juchong/ADXRS450-FRC-Gyro-Board/Documentation/2017/IMG_8723.JPG

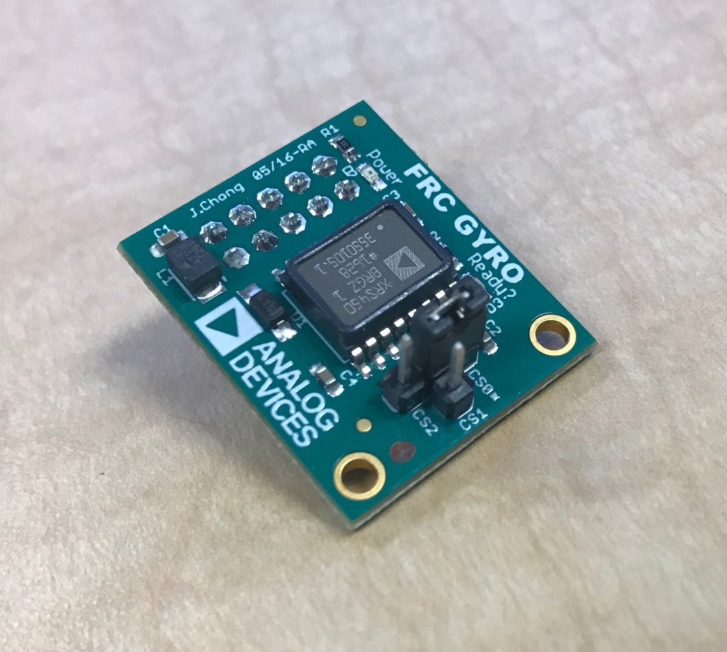
Documentation/2017/IMG_8723.JPG
